Affan-ahmed0/ODT2026-CapstoneProject-LaserTag/Media/Final/20260420_152249.jpg

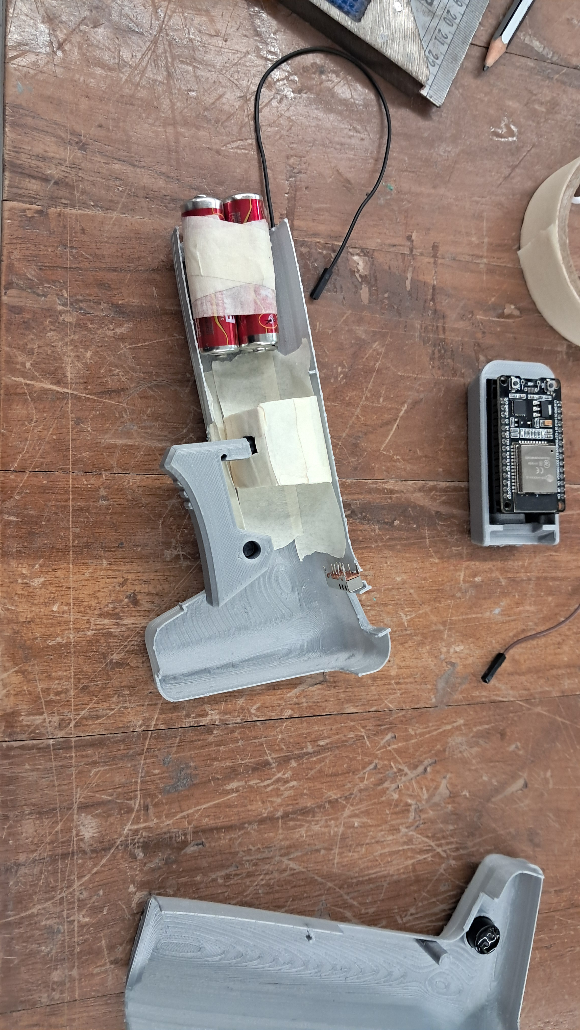
Media/Final/20260420_152249.jpg
