Affan-ahmed0/ODT2026-CapstoneProject-LaserTag/Media/Final/20260420_173724.jpg

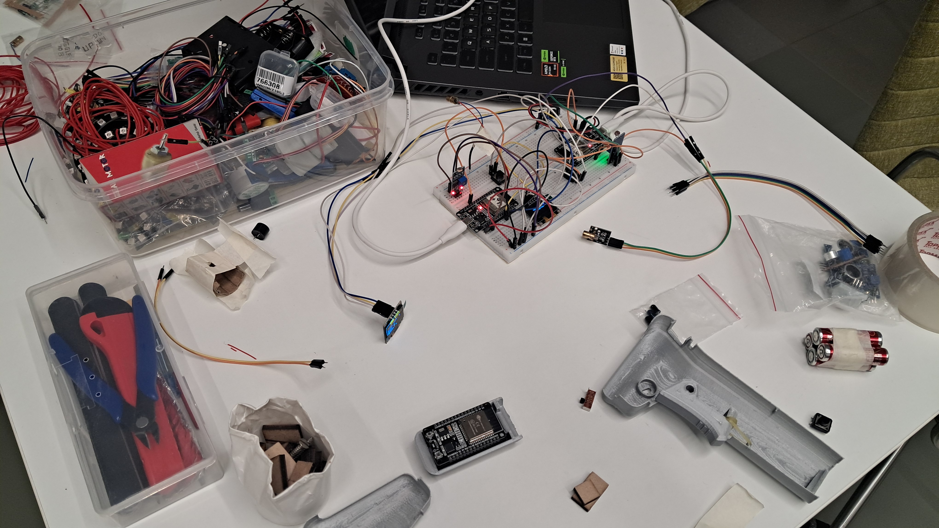
Media/Final/20260420_173724.jpg
