Affan-ahmed0/ODT2026-CapstoneProject-LaserTag/Media/Final/20260420_174153.jpg

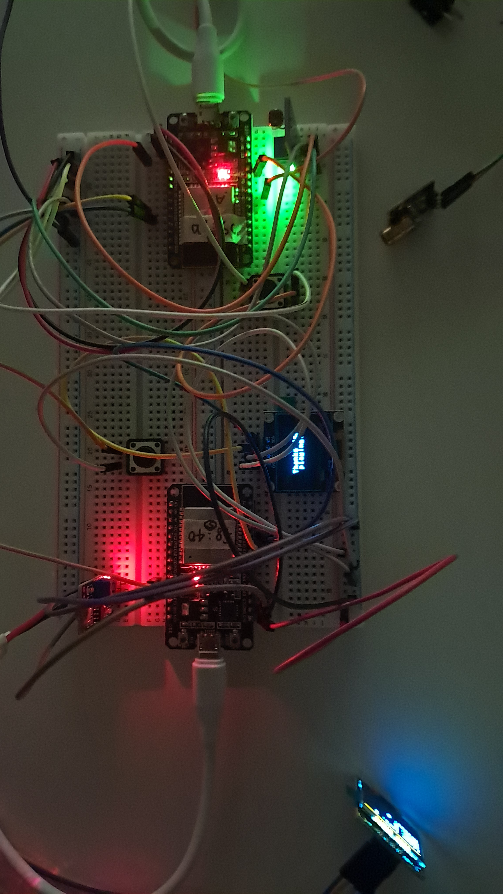
Media/Final/20260420_174153.jpg
