Affan-ahmed0/ODT2026-CapstoneProject-LaserTag/Media/Final/20260421_000429.jpg

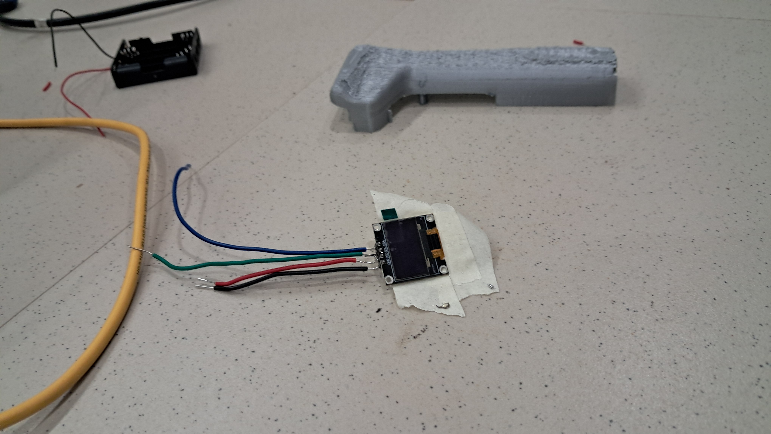
Media/Final/20260421_000429.jpg
