Affan-ahmed0/ODT2026-CapstoneProject-LaserTag/Media/Final/20260421_000433.jpg

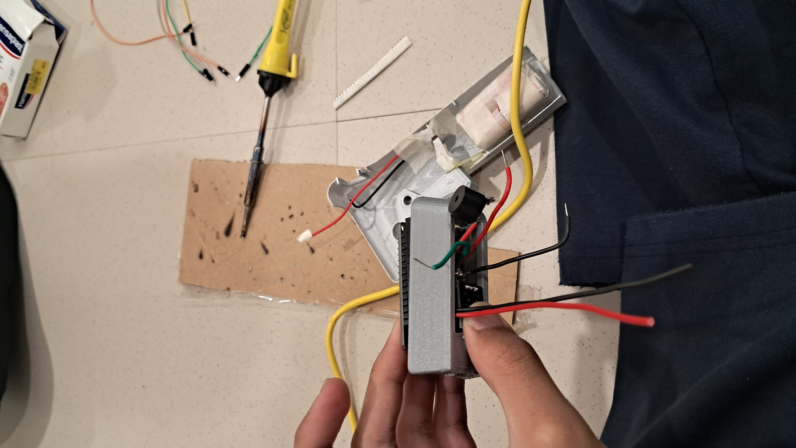
Media/Final/20260421_000433.jpg
