Affan-ahmed0/ODT2026-CapstoneProject-LaserTag/Media/Final/20260421_105037.jpg

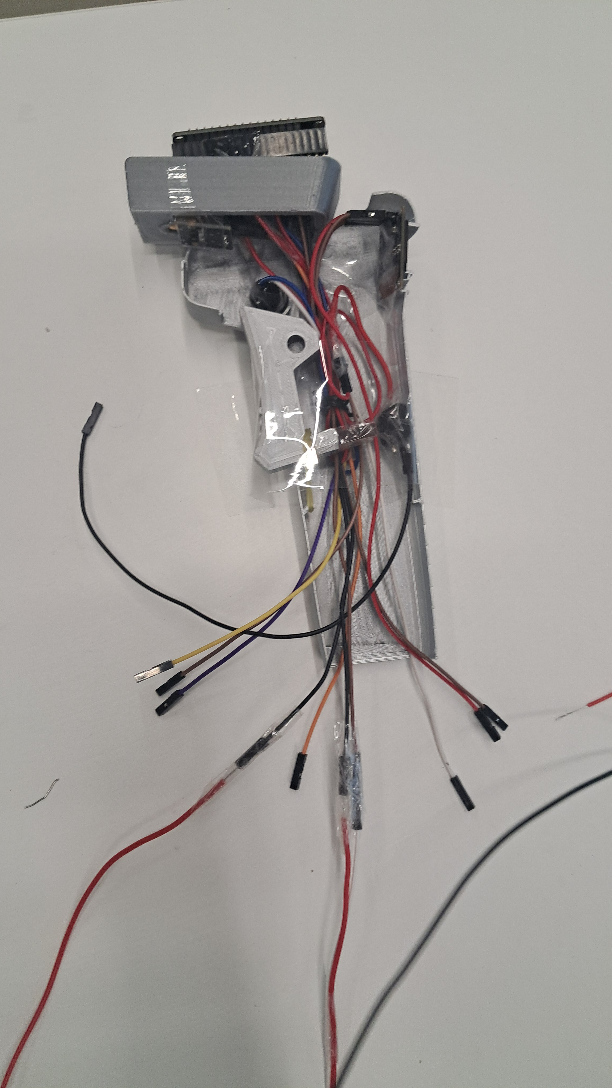
Media/Final/20260421_105037.jpg
