Affan-ahmed0/ODT2026-CapstoneProject-LaserTag/Media/Week2/Top View.png

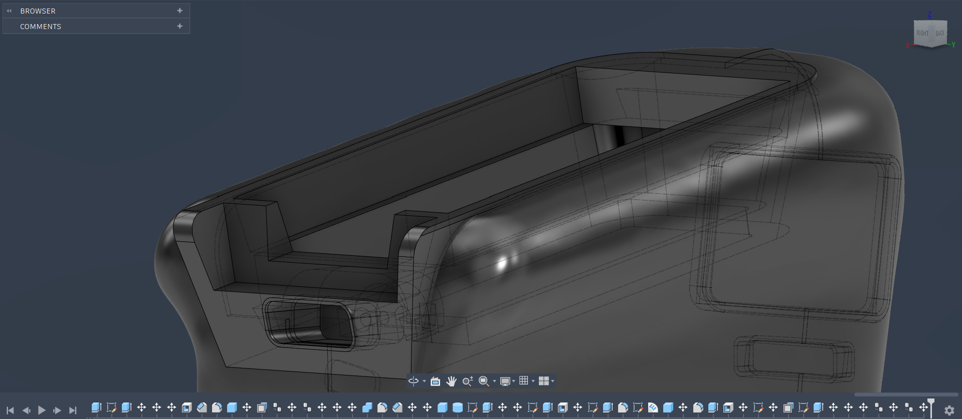
Media/Week2/Top View.png
