Affan-ahmed0/ODT2026-CapstoneProject-LaserTag/Software Details/A2/2. OLED, Buzzer, Neopixel, Laser/2.1 oled_test1.py

import machine, ssd1306
import framebuf
import utime

i2c = machine.I2C(scl=machine.Pin(19), sda=machine.Pin(21))
display = ssd1306.SSD1306_I2C(128, 64, i2c)

display.fill(0)

h = [
0x00, 0x00, 0x00, 0x00, 0x00, 0x00, 0x00, 0x00, 0x00, 0x00, 0x00, 0x00, 0x00, 0x00, 0x00, 0x00,
0x00, 0x00, 0x00, 0x00, 0x00, 0xE0, 0x07, 0x00, 0x07, 0xF8, 0x3F, 0xE0, 0x0F, 0xFE, 0x7F, 0xF0,
0x1F, 0xFE, 0x7F, 0xF8, 0x1F, 0xFF, 0xFF, 0xF8, 0x3F, 0xFF, 0xEF, 0xF8, 0x3F, 0xFF, 0xCF, 0xFC,
0x3F, 0xFF, 0xC7, 0xFC, 0x3F, 0xFF, 0x87, 0xFC, 0x3F, 0xFF, 0x83, 0xFC, 0x3F, 0xFF, 0x93, 0xFC,
0x1F, 0xE7, 0x31, 0xF8, 0x1F, 0xE7, 0x39, 0xF8, 0x10, 0x02, 0x38, 0x00, 0x08, 0x1A, 0x7C, 0x00,
0x07, 0xF8, 0x7F, 0xE0, 0x03, 0xF8, 0xFF, 0xC0, 0x01, 0xFC, 0xFF, 0x80, 0x00, 0xFD, 0xFF, 0x00,
0x00, 0x7F, 0xFC, 0x00, 0x00, 0x1F, 0xF8, 0x00, 0x00, 0x07, 0xE0, 0x00, 0x00, 0x03, 0xC0, 0x00,
0x00, 0x01, 0x00, 0x00, 0x00, 0x00, 0x00, 0x00, 0x00, 0x00, 0x00, 0x00, 0x00, 0x00, 0x00, 0x00
]
heart = bytearray(h)

def anim():
    del h[-1]
    


while True:
    display.text(' ', 0, 0)
    fb = framebuf.FrameBuffer(heart, 32, 32, framebuf.MONO_HLSB)
    display.blit(fb, 0, 0)
    display.show()
    anim()
    utime.sleep(0.01)
    heart = bytearray(h)

    
    
